Ashassins/NYAKB/ECE 362/ECE 362 Lectures/10-Advanced-Timers-Outputs.pdf

# Advanced Timers

# ECE 362 https://engineering.purdue.edu/ece362/

© 2021, Rick. All Rights Reserved. Redistribution Prohibited.

# Reading Assignment

# - Reading assignment:

– Textbook, Chapter 15, “General-purpose Timers”, pages 373 – 414.

# – Family Reference Manual, Chapter 17, "General

purpose timers (TIM2 and TIM3)", pages 377 – 443.

# Future Reading Assignment

- Textbook, Chapter 22, Serial Communication Protocols, pp. 527 – 598
– It’s a long chapter.
– Let’s first look at Section 22.3, SPI, pp. 568–577.
– Don’t worry so much about the USB section.
- Read that only if you’re curious.
- Your development board has no USB interface.
– There are some USB provisions in the STM32F091, but would take much work.
- Other books are better for understanding USB.

# GPIO Alternate Function

- Recall that the 2-bit fields in the GPIOx_MODER can take on four values to define a pin mode: – 00: Pin is an input.
– 01: Pin is an output.
– 10: Pin uses an alternate function.
– 11: Pin is an analog input.
- Today, we’ll start using the alternate function codes.
– Configured by four-bit fields in the GPIOx_AFRL and GPIOx_AFRH. – Datasheet, page 41, table 14, Alternate functions for Port A.
– Datasheet, page 42, table 15, Alternate functions for Port B.
– ...
- Configuring a pin for AF means you cannot use that pin for general purpose I/O. – See FRM, Figure 20, page 163.

# To set GPIO alternate function

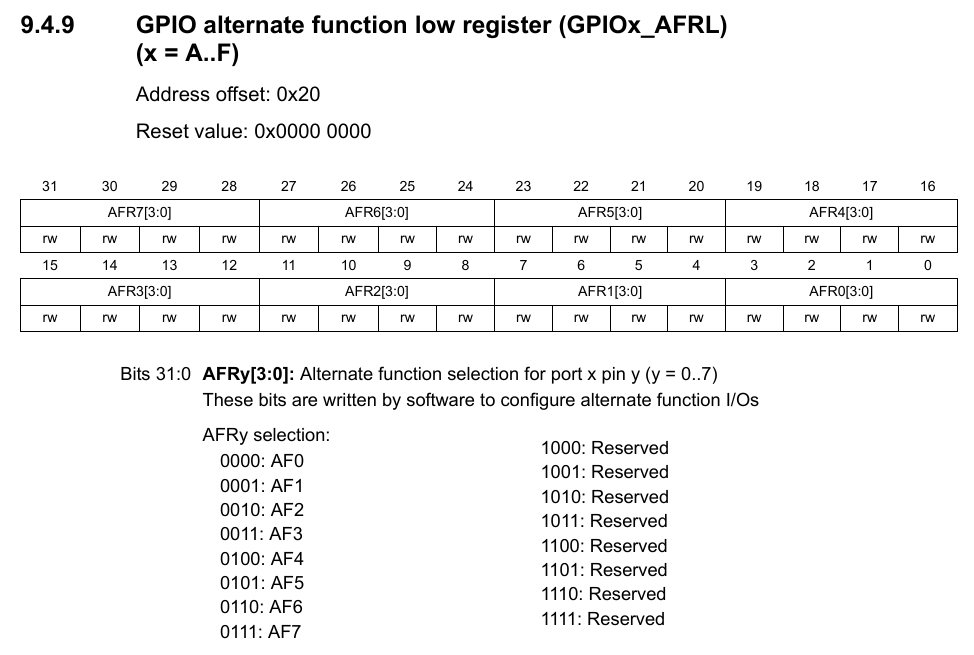
[picture p90: figure]

# - Two 32-bit AFR registers per port

named AFRL/AFRH.
- Four bits per pin.

## – e.g., to set PA0 to use timer 2, channel 1:

## - GPIOA->AFRL_AFR0[3:0] = 0010

– e.g., to set PB14 to use timer 15,

## channel 1:

## - GPIOB->AFRH_AFR6[3:0] = 0001

- (14 – 8 == 6)

## – Where did these numbers come from?

## - Tables 14 – 19

# Port A alt funcs: Datasheet pg 41

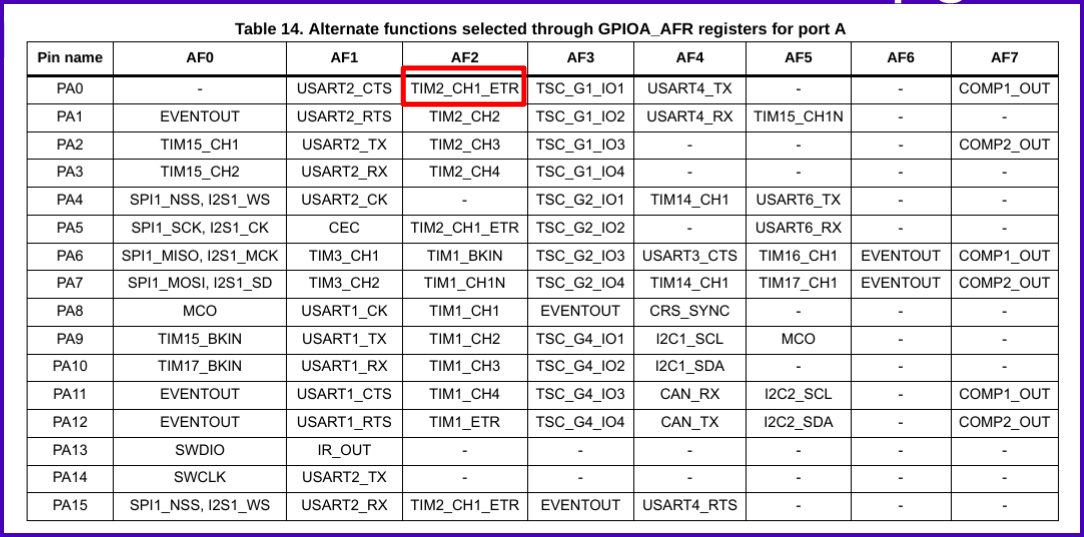
[picture p91: figure]

# Port B alt funcs: Datasheet, pg 42

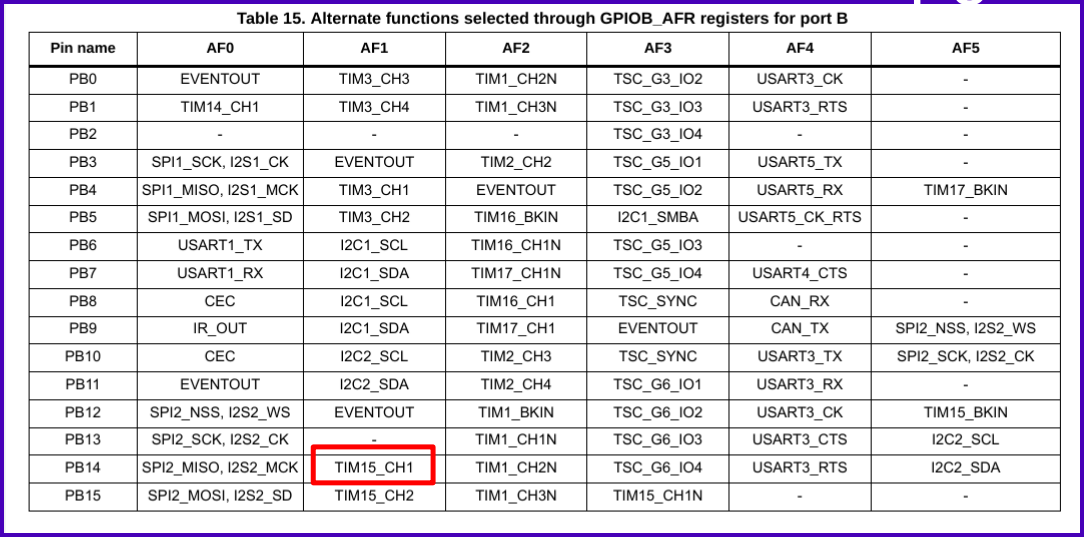
[picture p92: figure]

# Accessing AFRx registers with C

- It’s complicated.

# - You can refer to values with symbols like this:

# GPIO_AFRL_AFRL0 == 0x0000000F GPIO_AFRH_AFRH5 == 0x00F00000

# - It’s often easier to do it manually (e.g.: PB11: AF2):

# – GPIOB->AFR[1] &= ~(0xf << (4*(11-8))) – GPIOB->AFR[1] |= 0x2 << (4*(11-8))

# Timers: There are many

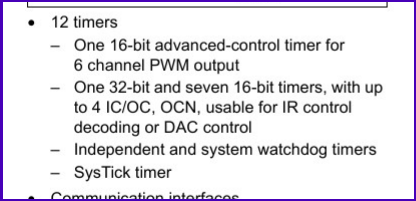
[picture p93: figure]

# - Start with the STM32F091xBC

datasheet page 1.

# “How should I choose?”

# - Start with the STM32F091xBC datasheet…

– page 34, table 13, pin definitions.
- See the "Alternate functions" column.

# – pages 41 – 44, table 14 – 19, Alternate functions for

Ports A, B, C, D, and F.

# – "What about Port E?"

- We don’t actually have a Port E on a 64-pin STM32F091.

# “If I want a certain function, how do I chose a pin for it?”

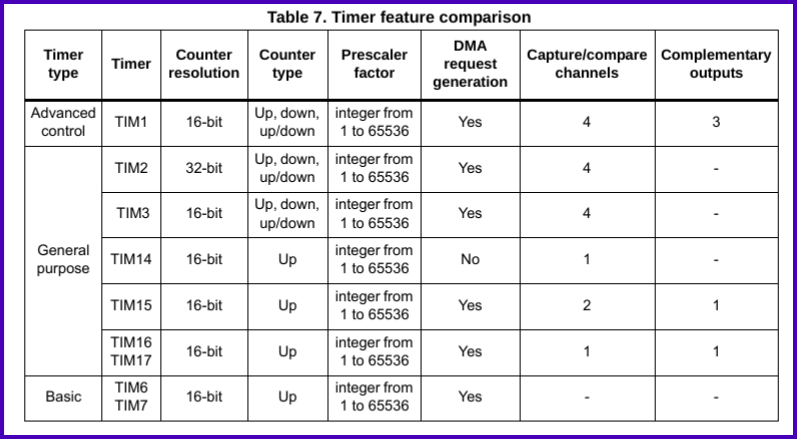
[picture p94: figure]

# - Start with the STM32F091xBC

datasheet again.

# – page 21, table 7, timer feature comparison

# “What pins should we start with?”

- From datasheet, table 13, pin definitions...

– User push button SW2 (PA0) can be connected to TIM2_CH1_ETR [Timer 2, channel 1 (and external trigger)] – Red LED (PC6) can be connected to TIM3_CH1 [Timer 3, channel 1] – Yellow LED (PC7) can be connected to TIM3_CH2 [Timer 3, channel 2] – Green LED (PC8) can be connected to TIM3_CH3 [Timer 3, channel 3] – Blue LED (PC9) can be connected to TIM3_CH4 [Timer 3, channel 4]
- So, let’s look at Timers 2 and 3.

# Timer groups 2 and 3

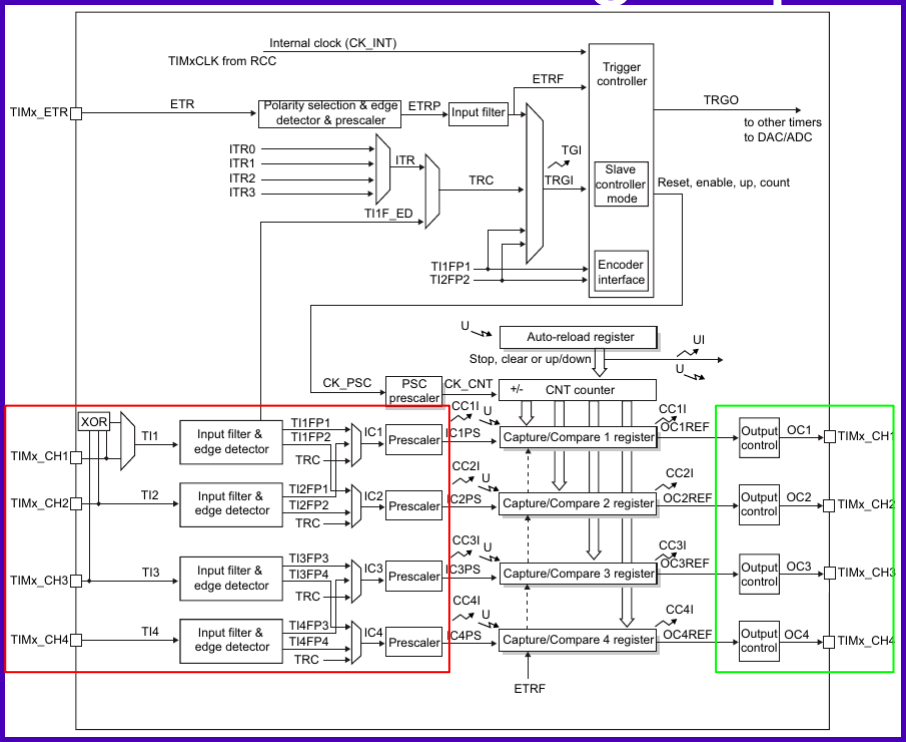
[picture p95: figure]

# - This is what either timer

2 or timer 3 look like.

# – Each one contains four

timer channels.

# - Each can:

## – measure input - count events - pulse length – generate output - toggle - PWM: Pulse Width Modulation – generate interrupts

# How do TIM2/TIM3 work?

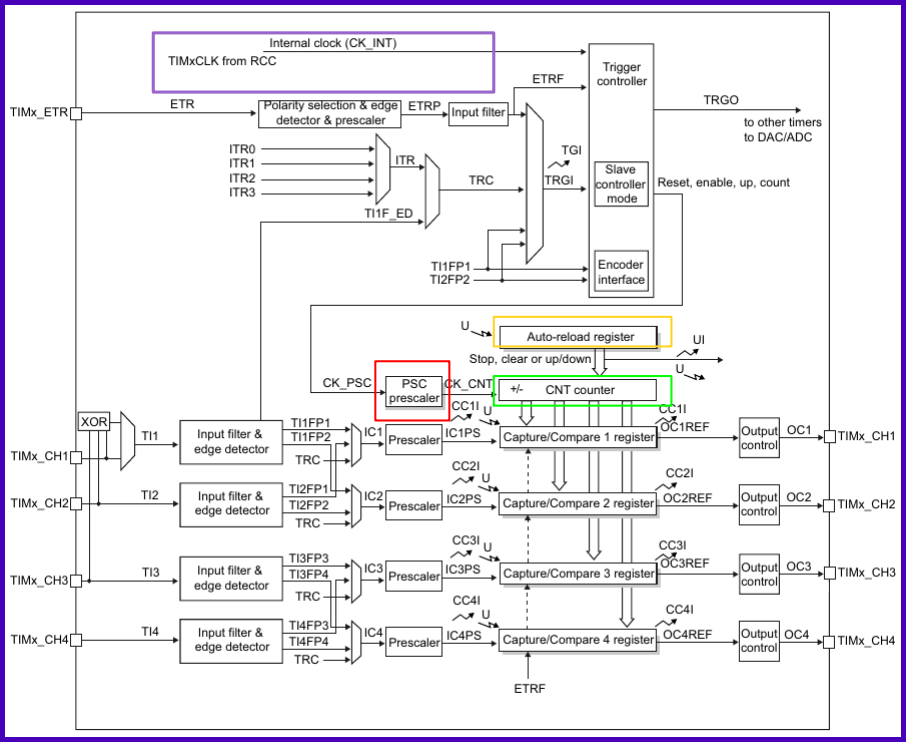
[picture p96: figure]

# - Each has a free-running counter (CTR) which is 16-

bit (TIM3) or 32-bit (TIM2).

# – 16-bit prescaler for input

clock (PSC).
- e.g. divide input clock by N.
- System clock is default clk.

# – Auto-reload register (ARR)

## - Can count up from 0 to ARR - Can count down from ARR to 0

- Can count up, down, up,

## down… 0 – ARR – 0 …

# Configuring a timer for "output"

# - Let’s look at output first. In this mode we:

# – configure a GPIO pin for an alternate function that connects it to a timer

rather than its ODR.

# – set up the prescaler (PSC) – set up the auto-reload register (ARR) – set the direction/mode of the counter (CR1 DIR) – set the output compare mode (CCMRn OCcM) – enable the "channel" the pin is connected to (CCER) – enable the timer’s counter (with the CR1 CEN bit)

# Counter modes

# ARR

# time ARR

# time ARR

# time

UP

# DOWN

# UP/DOWN

0

0

0

# Counter mode configuration

# - Set with the TIMx_CR1 register:

- CMS: Center-aligned (up/down) mode selection.
– Non-zero value enables up/down mode.

# - DIR: Direction: 0: counts up, 1: counts down

- CEN: Counter enable: 1: enable timer.

## – Set this one last. SET CEN LAST!

# How do channels work?

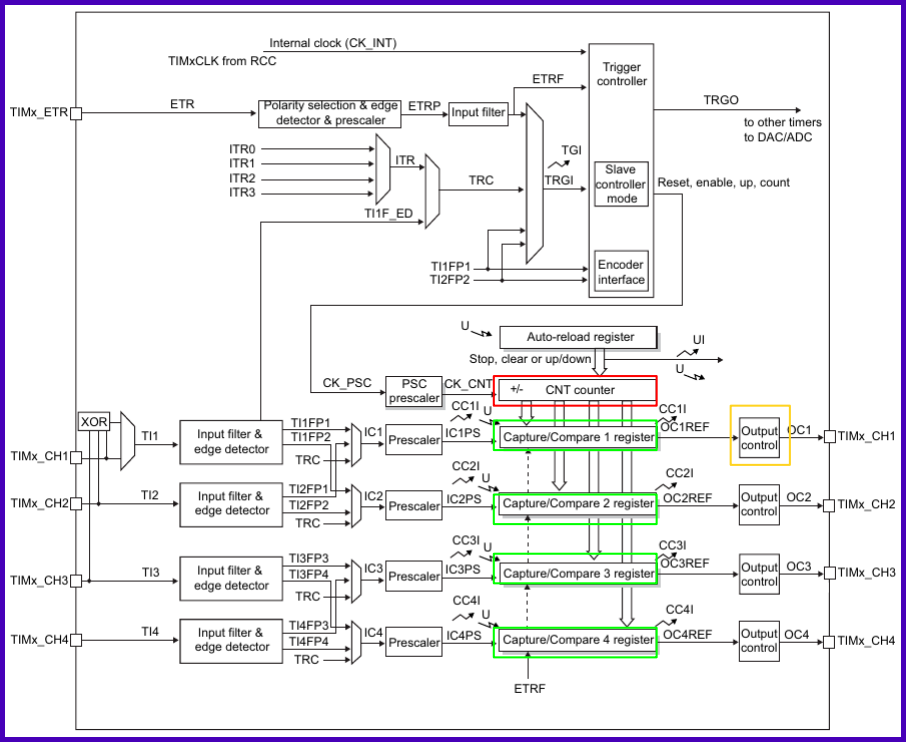
[picture p97: figure]

# - Each has a counter compare register

(CCRx).

# – Each is continually compared to the

counter (CTR).
– When CCRx = CTR,

# something happens to OCxREF (output

channel reference).

# Timer Output Modes

## - Configured with the two CCMRs (Capture/Compare Mode Registers)

## - CC1S: direction of channel:

– 00: output, 01: input mapped on TI1, 10: input mapped on TI2, 11: input mapped on TRC.

## - OC1M: output compare mode:

## – 001: Logic high if CNT = CCR – 010: Logic low if CNT = CCR – 011: Toggle if CNT = CCR – 110: PWM output mode 1: Logic high if CNT < CCR, else logic low

# Remember to enable the channels

# - Use the TIMx_CCER (capture/compare enable register)

# - CCxE: enable the channel

# Example: count up, active high

# ARR

# time

0

# CCRx

# time

0

# Output

# Each CCR is continually comparing its value

with the free-running counter.

# When it matches, the operation (go high) happens

# Example: count up, toggle mode

# ARR

# time

0

# CCRx

# time

0

# Output

# Each CCR is continually comparing its value

with the free-running counter.

# When it matches, the operation (toggle) happens

# Example: count up, toggle mode

# ARR

# time

0

# CCRx

# time

0

# Output

# Changing the CCRx value changes the offset

into the count when the output toggles.

# Example: up/down, toggle mode

# ARR

# time

0

# CCRx

# time

0

# Output

# Up/down mode is referred to as "Centered Mode"

# Example: up/down, toggle mode

# ARR

# time

0

# CCRx

# time

0

# Output

# Changing the CCRx value widens the active cycle of the wave, but it stays "centered"

# Example: count up, PWM mode 1

# ARR

# time

0

# CCRx

# time

0

# Output

# PWM output mode is an easy way of

configuring a variable "duty cycle" output.

# Example: count up, PWM mode 1

# ARR

# time

0

# CCRx

# time

0

# Output

# As CCRx value is decreased, the

"duty cycle" is decreased proportionally.

# How do I program this???

#include "stm32f0xx.h"

int main(void)
{
// Enable Port C
RCC->AHBENR |= RCC_AHBENR_GPIOCEN;

// Set the mode for PC8 for "alternate function" GPIOC->MODER &= ~(3<<16);
GPIOC->MODER |= 2<<16;

// Set the alternate function for PC8
// PC0-7 are on AFR[0], 8-15 are on AFR[1] GPIOC->AFR[1] &= ~0xf;
GPIOC->AFR[1] |= 0;

// Enable the system clock for timer 3 RCC->APB1ENR |= RCC_APB1ENR_TIM3EN;

// Counting direction: 0=up, 1=down
TIM3->CR1 &= ~TIM_CR1_DIR; // clear it to count up

// Set prescaler output to 4kHz (48MHz/12000) TIM3->PSC = 12000 – 1;

// Auto-reload 4000
TIM3->ARR = 4000 – 1;

// Any value between 0 and 4000.
TIM3->CCR3 = 3456;

// Channel 3 of the timer is configured in CCMR2. // Set the bits to select toggle mode (011) TIM3->CCMR2 &= ~TIM_CCMR2_OC3M_2; // Turn off bit 2.
TIM3->CCMR2 |= TIM_CCMR2_OC3M_1 | TIM_CCMR2_OC3M_0;

// Enable output for channel 3 active-high output TIM3->CCER |= TIM_CCER_CC3E;

// Enable timer 3
TIM3->CR1 |= TIM_CR1_CEN;

for(;;)
asm(“wfi”);

return 0;
}
Adapted from Textbook, page 380.

# This will blink the

green LED.

# Register summary

- See Family Reference Manual, table 60, page 442...

# - TIMx_CR1: Control Reg - TIMx_CCMR1/2: Capture/Compare Mode Reg - TIMx_CCER: Capture/Compare Enable Reg - TIMx_CNT: 16- or 32-bit Free-running counter - TIMx_PSC: 16-bit Prescaler Reg - TIMx_ARR: Auto-Reload Reg - TIMx_CCRx: Capture/Compare Reg

- RCC_APB1ENR: Location of the TIM3EN bit.

# Full view of Timer 2/3 again

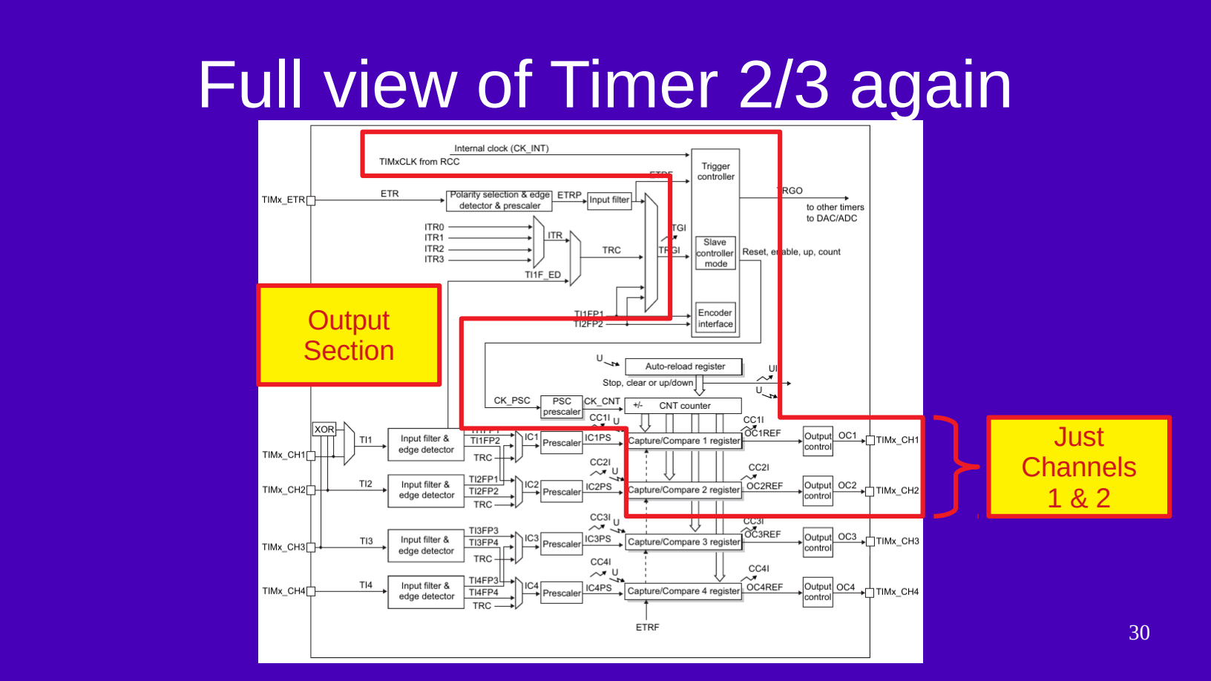
[picture p98: page 30]

# Output Section

# Just Channels

1 & 2

# Output config register arrangement

# Prescaler

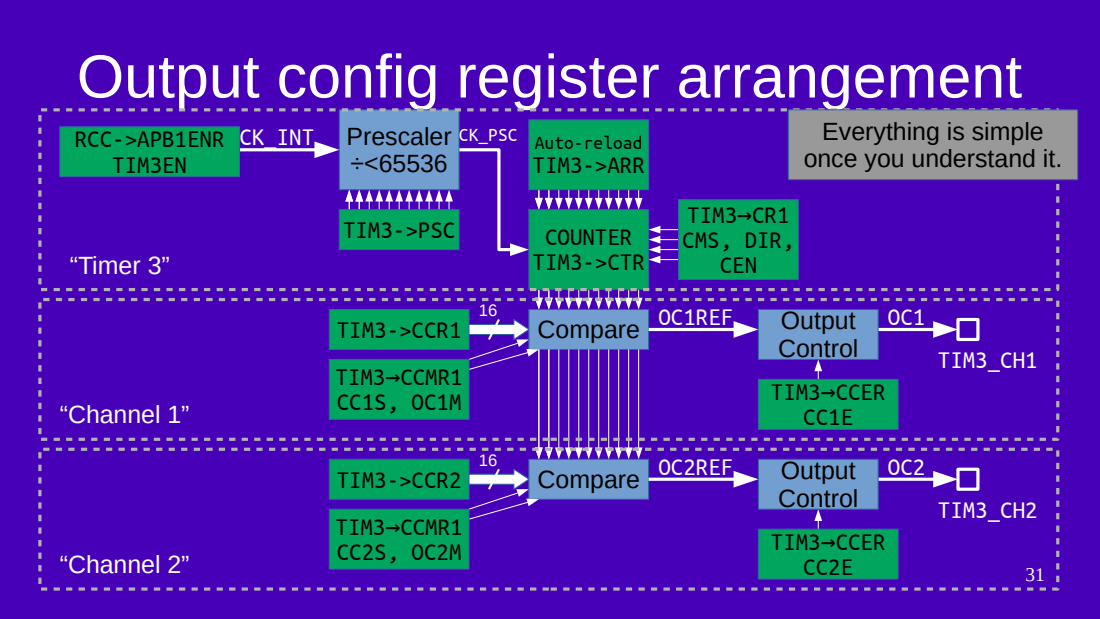
[picture p99: page 31]
CK_INT; CK_PSC; Auto-reload; TIM3->ARR; TIM3->PSC; COUNTER; TIM3->CTR; TIM3 CR1 →CR1 CMS, DIR, CEN; TIM3->CCR1; Compare; TIM3 CCMR1 →CR1 CC1S, OC1M; OC1REF ¹⁶; RCC->APB1ENR TIM3EN; TIM3 CCER →CR1 CC1E; Output Control; TIM3_CH1; TIM3->CCR2; TIM3 CCMR1 →CR1 CC2S, OC2M; OC2REF ¹⁶; TIM3 CCER →CR1 CC2E; TIM3_CH2; “Timer 3”; “Channel 1”; “Channel 2”

Everything is simple
once you understand it.
