Ashassins/NYAKB/ECE 362/ECE 362 Lectures/12-DAC.pdf

Digital-to-Analog Conversion

ECE 362
https://engineering.purdue.edu/ece362/

© 2021, Rick. All Rights Reserved. Redistribution Prohibited.

Reading Assignment

- Textbook, Chapter 21, Digital-to-Analog Conversion, pp. 507 – 526. – Read this first.
- FRM, Chapter 14, Digital-to-analog converter (DAC), pp. 269 – 281. – Scan. Learn basics like I/O registers, enabling, use.
- Textbook, Chapter 20, Analog-to-Digital Conversion, pp. 481 – 506. – Read this later.
- FRM, Chapter 13, Analog-to-Digital converter (ADC), pp. 229 – 268. – Scan this later. Learn basics like I/O registers, enabling, use.

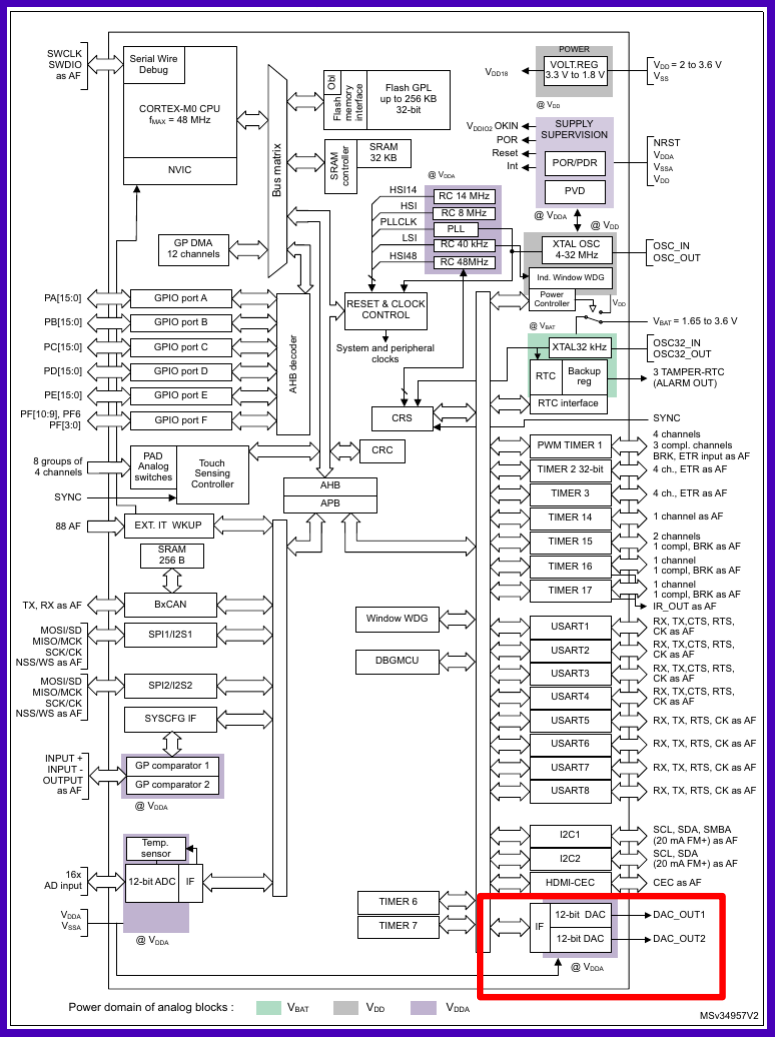
[picture p113: figure]

The STM32F091

- Digital-to-Analog Converter
– 2 external channels (DAC_OUT1, DAC_OUT2)
- What pins are those?
– You can look those up. You know how. – Or pay close attention to the lecture.
– 0 – 3.6V conversion range
- Our voltage reference is about 3.0V – 12-bit resolution, by default
- 8-bit resolution too
– right-aligned (default) or left-aligned

DAC Block Diagram

Page 270 of the

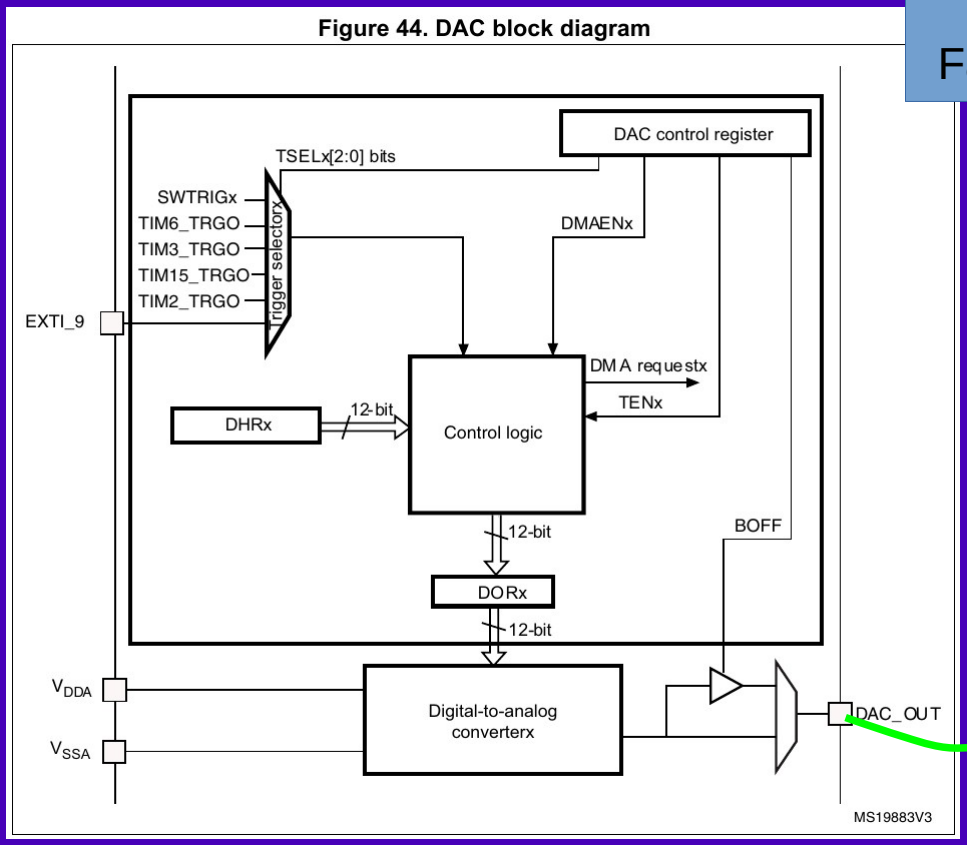
[picture p114: figure]

Family Reference Manual

- A Data Output Register (DORx) holds a value that is converted to an analog voltage between 0 and 3V.
- CPU can’t write directly to DORx.
- Must write to DHRx.
– "Data Holding Register"
– A trigger will move DHRx to DORx.

DAC Output Connection

- Some analog pin(s) can be output.

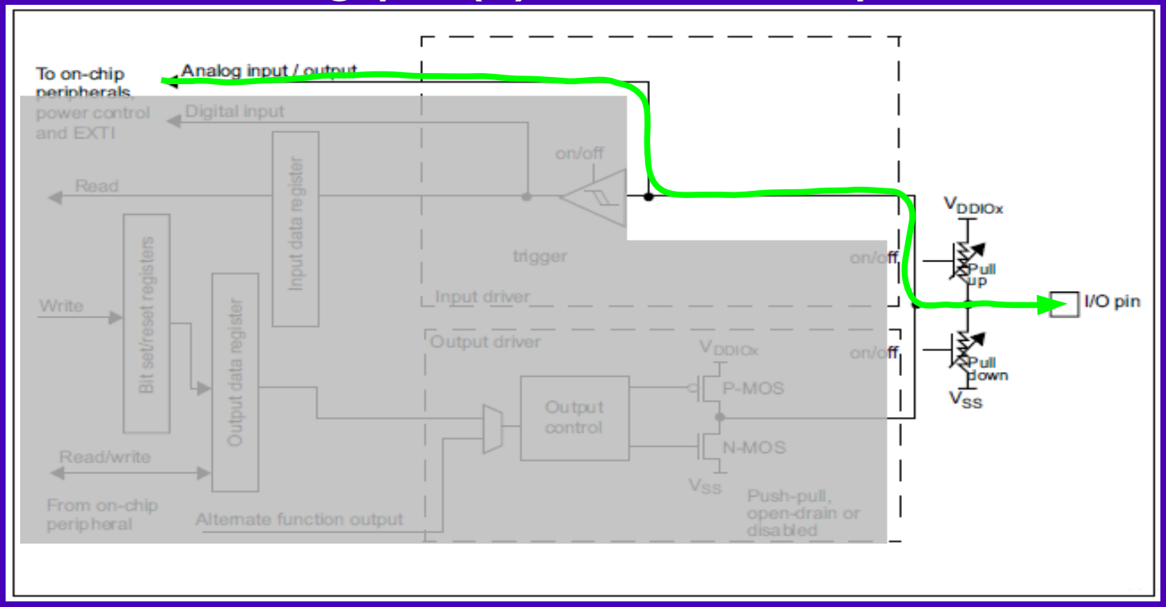
[picture p115: figure]

Port MODER

- 16 2-bit values determine, input, output, or special operation. – 00: Port pin is used for input
– 01: Port pin is used for output
– 10: Port pin has an alternate function
– 11: Port pin is an analog pin

How does a DAC work?

- And what does this left-aligned or right-aligned mean?

Let’s talk about number systems

- A group of bits can be used to represent arbitrary things
- A character, a number, an image, …
- "Integers" have a well-known format
128 | 64 | 32 | 16 | 8 | 4 | 2 | 1
0 | 1 | 0 | 1 | | 1 | 0 | 1
... | 1
= 93
- Ellipsis goes off to the left.
- What if we added another bit to the right?

Binary fractions

- We can let a 16-bit value represent anything we want, so let’s let the upper 8 bits represent an integer, and let the lower 8 bits represent fractional powers of 2
- The dot is called a "binary point"
- Representation, below, is called "fixed point", Q8.8, or just Q8.

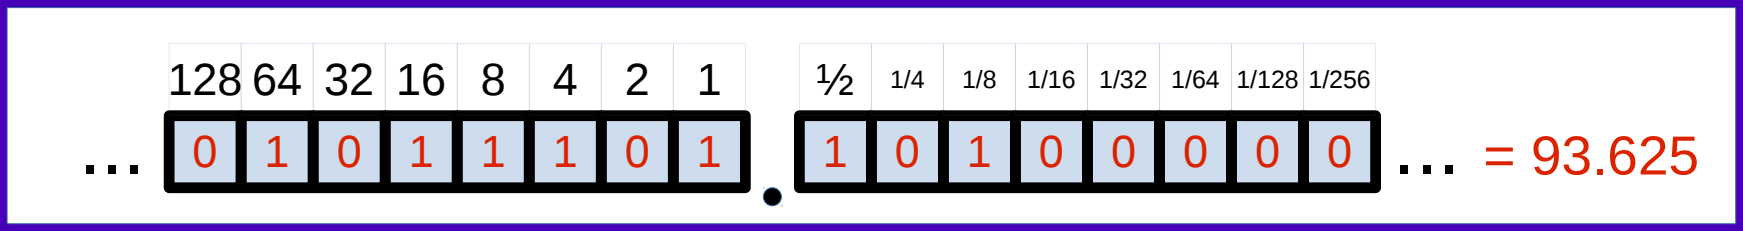
[picture p116: figure]

- Standard binary addition and subtraction still works.
- Multiplication needs a correcting shift afterward.

Fixed point is inexact

- Sums of fractional powers of 2, OK.
– e.g. We can express 3.75 as 00000011.1100….
- Anything else has rounding errors. e.g. 93.1.
- 93 + 1/8 is 93.125 (too big)
- 93 + 1/16 + 1/32 = 93.9375 (too small)
- 93 + 1/16 + 1/32 + 1/256 + 1/512 = 93.099609375 (too small, but closer)

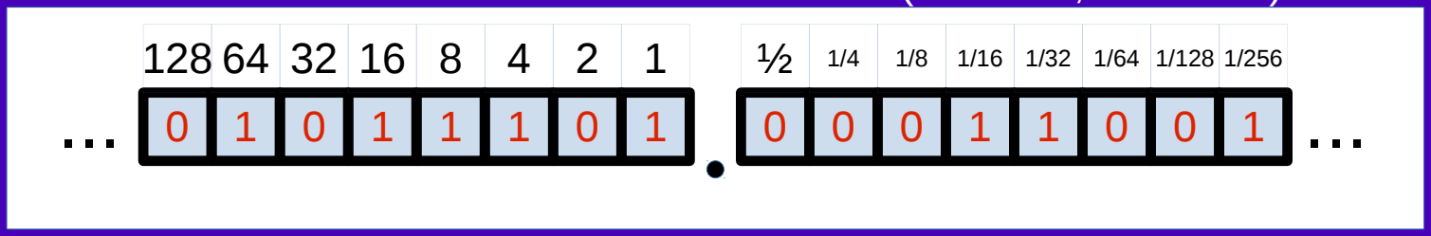
[picture p117: figure]

- The precise binary value would repeat forever: 01011101.000110011001100...

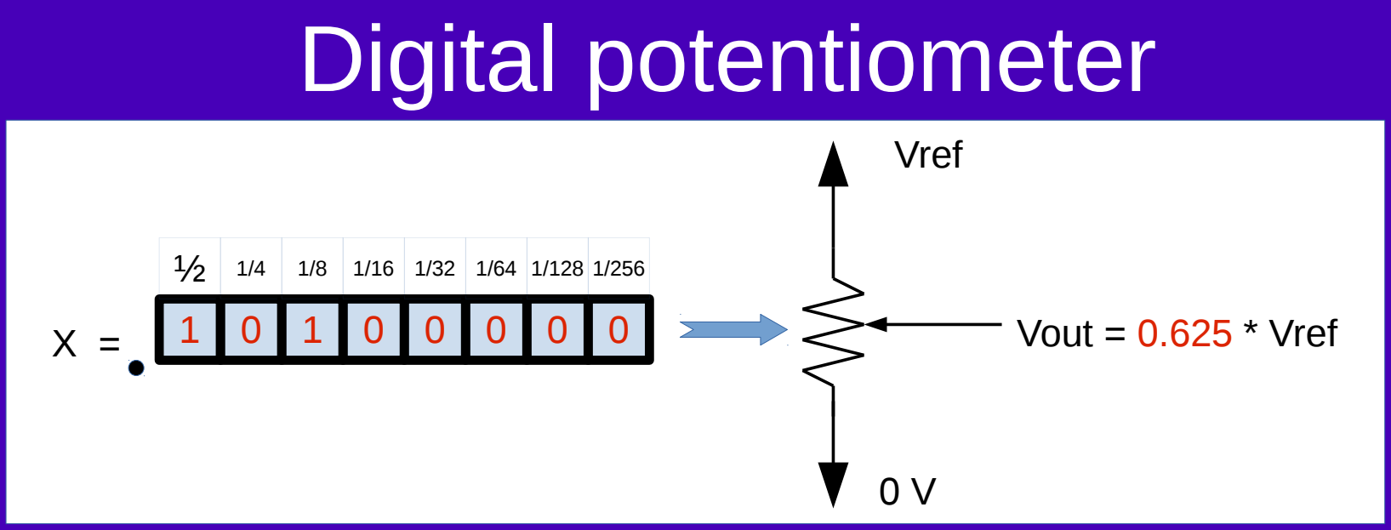
[picture p118: figure]
Digital potentiometer; Vref; Vout = 0.625 * Vref

- We want hardware that can convert a binary fraction to a voltage.
– The most significant bit of the fraction is “worth” half the reference voltage. – A “left-aligned” conversion value is, effectively, a binary fraction.
- How can we build such a thing?

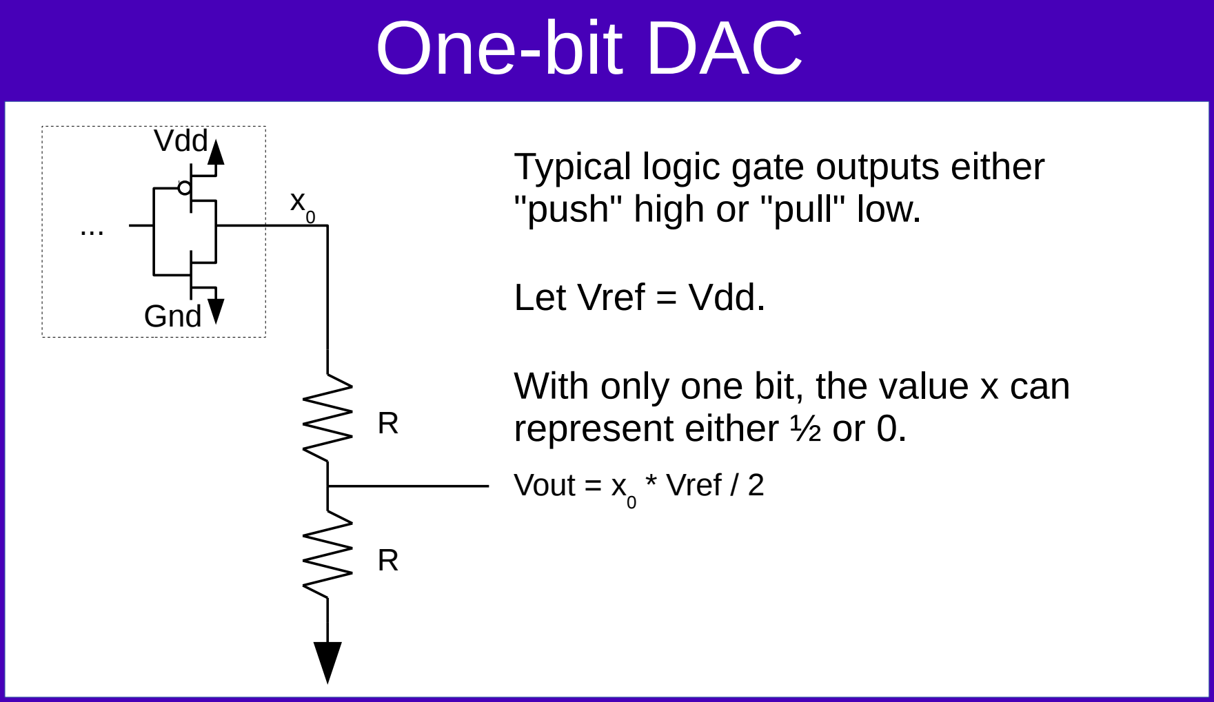
[picture p119: figure]
One-bit DAC; Vout = x; * Vref / 2; Typical logic gate outputs either "push" high or "pull" low.; Let Vref = Vdd.; With only one bit, the value x can represent either ½ or 0.; Vdd; Gnd

Two-bit DAC

- X can have the values 0, ¼, ½, or ¾.

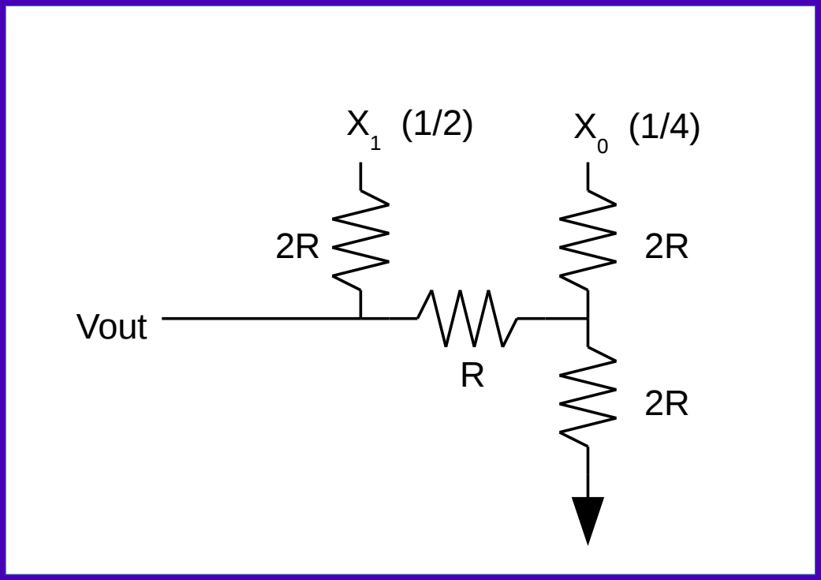
[picture p120: figure]
Vout

Many-bit DAC

- Add N more bits by adding N more R-2R resistors...

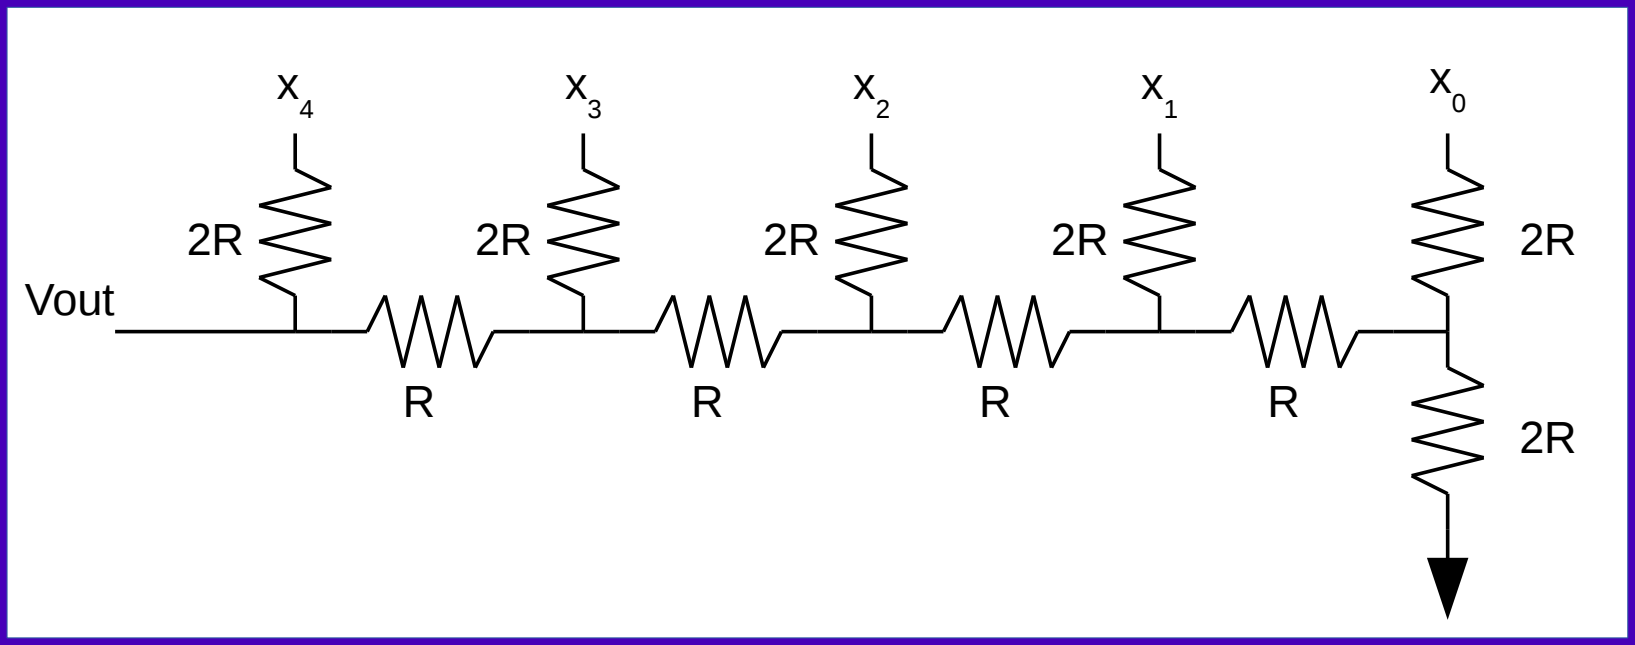
[picture p121: figure]
Vout

– This is called an R-2R resistor ladder.

DAC: How fast is the conversion?

- Speed of light.
– Some settling time required due to capacitance (and inductance) in circuit.
– Small glitches may be present due to differences in delays for turning on and off inputs into the resistor network.
- No iteration or convergence needed.

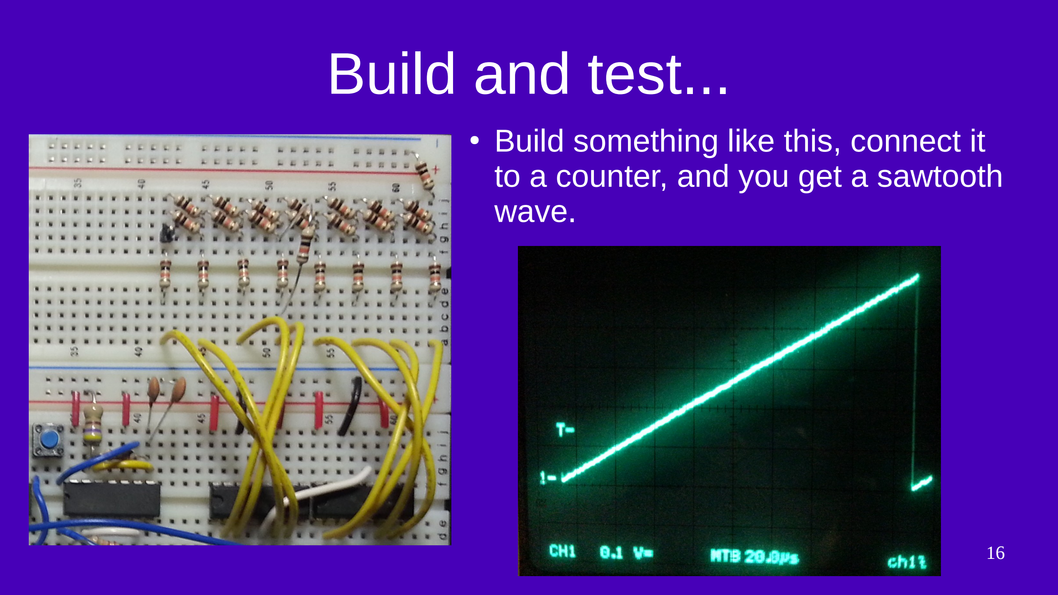
[picture p122: page 16]

Build and test...

- Build something like this, connect it to a counter, and you get a sawtooth wave.

Limits of DAC resolution

- Resistor tolerance is a limitation.
- Linearity of the output is only as good as the correctness of the resistor ratios.
- A single errant resistor can be problem.
- Small deviation will cause small error.
- Large deviation causes a non-monotonic output for the sawtooth wave.
- To ensure a monotonic sawtooth, each resistor should be less than +/- 1/(2N) its listed value. Why?
– Consider transition from 01111 to 10000.

●

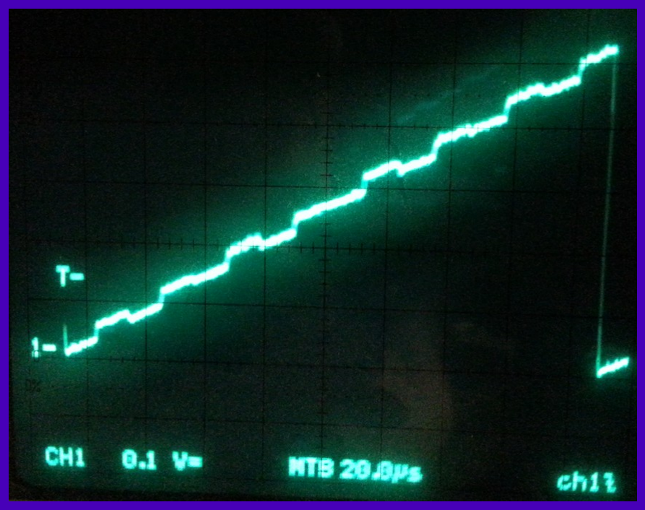
[picture p123: figure]

If most significant resistor was off by -1/(2⁵) the two values would be the same. – For an 8-bit DAC, resistor error must be < 0.4%
– For a 12-bit DAC, resistor error must be < 0.024%
- Helps if all resistors are on same silicon substrate!
– Which is what you have on your microcontroller.

Using the STM32 DAC

- There are two DACs on the STM32F091RCT6. – That can be used with two channels / pins.
- Cannot write directly to a DAC output register. – Instead, write a digital value to one of three "data holding registers."
– Some kind of trigger will copy it to the output register.

DAC Holding Registers

- 8-bit or 12-bit
- left-aligned or right-aligned
| xxxxxxxxxxxx

xxxxxxxxxxxx

| xxxxxxxx
31 | 23 | 15 | 7 | 0

DAC_DHR8R1: 8-bit, right-aligned, ch1

DAC_DHR12L1: 12-bit, left-aligned, ch1

DAC_DHR12R1: 12-bit, right-aligned, ch1

DAC Triggers

- Seven different trigger possibilities – 5 timers
– EXTI line9
– Software trigger
- Set with the DAC->CR TSEL1/2 fields. – 111 is the software trigger. Use this for now.

To trigger the DAC with a
software trigger
- Wait while the channel trigger is set. Once it is clear:
– Write a new value to a holding register.
– Set the trigger bit.

Example code to generate a sawtooth wave

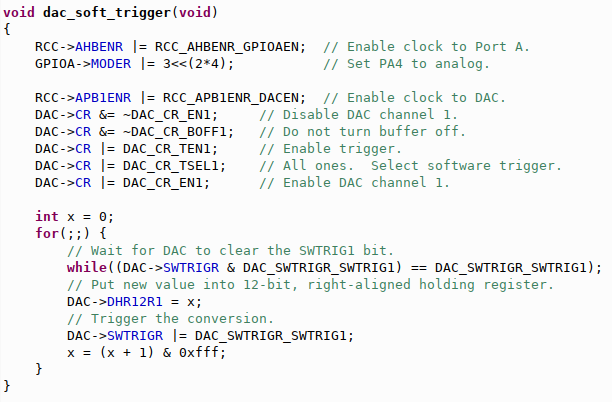
[picture p124: figure]

Scope view of unloaded pin

- 10x probes.
- 0.5V/div
- 500μs/div
- slight curve
on lower end

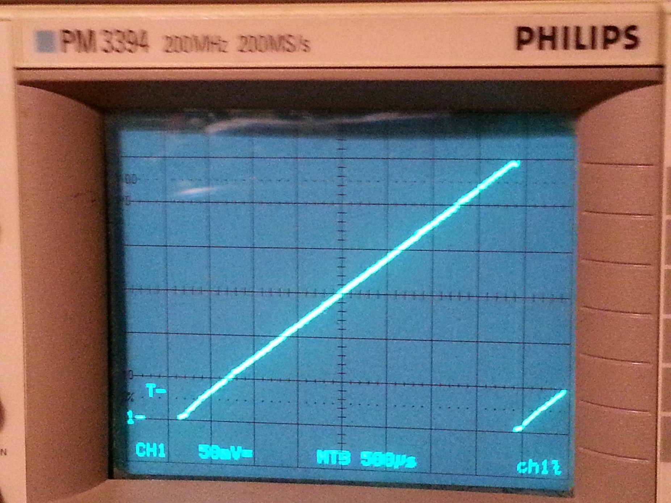
[picture p125: figure]

Conversion Examples

- Assume that VREF is 3.0 V.
- If the DAC’s right-aligned 12-bit data holding register was given the following values, what would the analog output voltage be?
- 0 ?
- 4095 ?
- 2047 ?
- 1023 ?

Output linearly related to DAC value

- Generally, the DAC output will be:

VOUT = VREF * N
4096

Some differences

- Lecture explanation of a DAC differs from that of the textbook and the FRM.
– Lecture: Each increment of the DAC value represents 1/4096th of VREF
- Minimum: 0 * VREF
- Maximum: 4095/4096 * VREF
– FRM: Each increment of the DAC value represents 1/4095th of VREF
- Minimum: 0 * VREF
- Maximum: 4095/4095 * VREF

Does this difference matter?

- The difference between the lecture and textbook version of a DAC is 1/4096th VREF – or about 0.024%. But nothing is exact... – There are deviations from linearity for the DAC.
– There is often a noise problem with the analog subsystems of the STM32F0.
- It’s about 0.02%. (More about this when we talk about ADC)
- Difference between this lecture and text doesn’t matter.
– You won’t notice a range of [0 – 2.9928] instead of [0 – 3.0]

What is BOFF1?

- An output buffer
can be turned off.
- You probably want
to leave it turned
on:
- DAC->CR &= ~
DAC_CR_BOFF1;

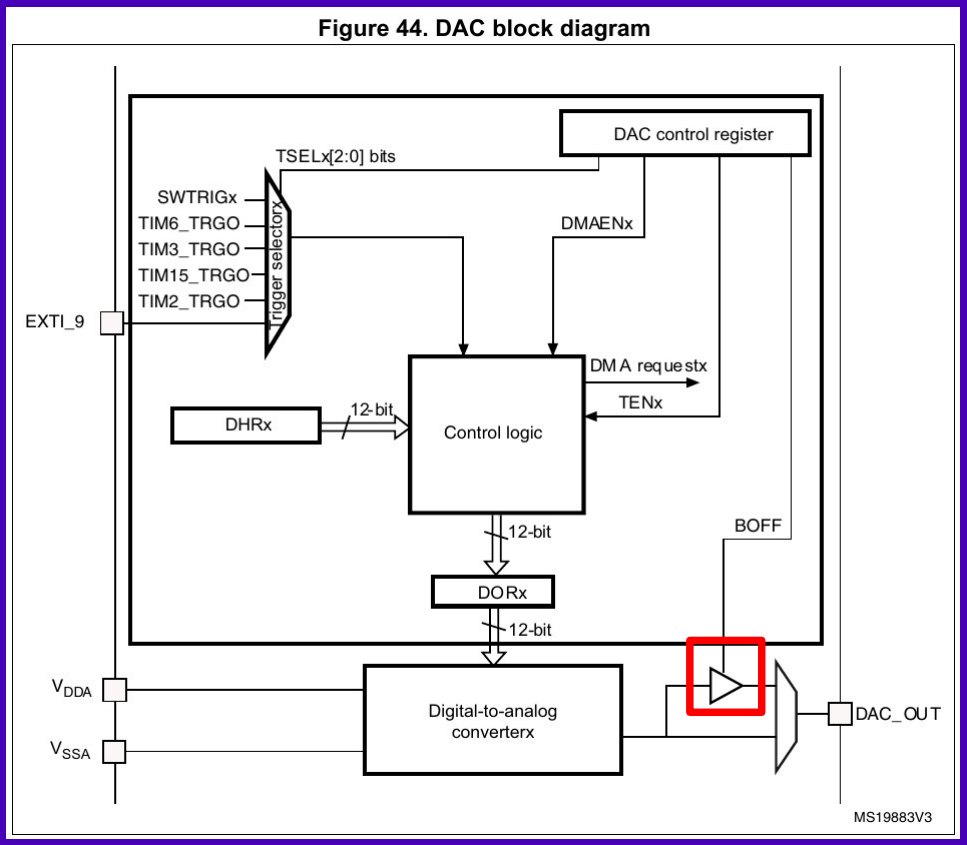
[picture p126: figure]

Why do we need a buffer?

- Recall the hand-built DAC circuit:

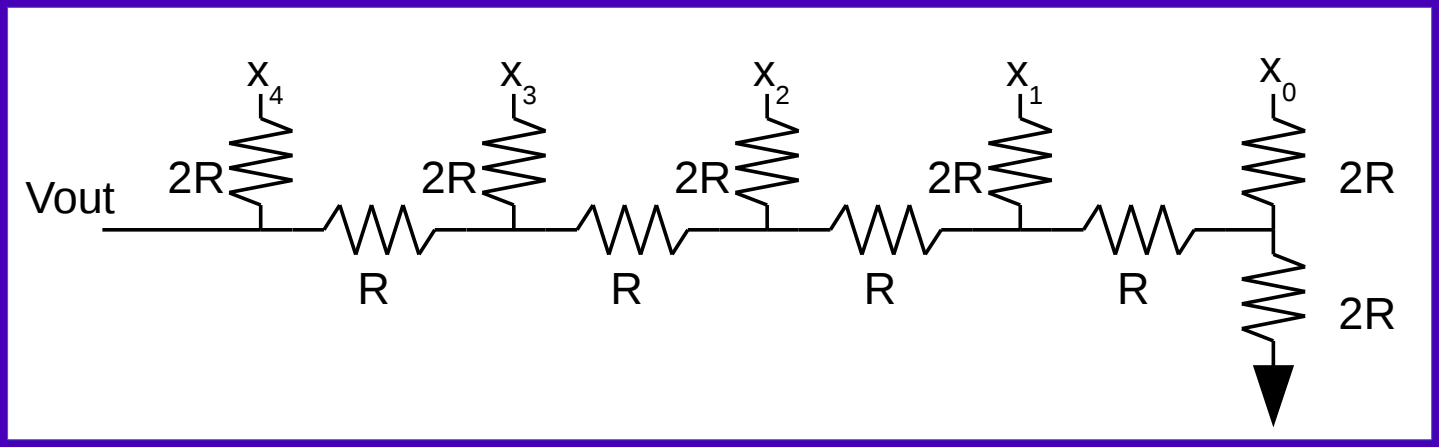
[picture p127: figure]
Vout

- What’s the impedance of Vout if R = 10KΩ?

Why would we turn buffer off?

- Maybe you want to use your own high-precision amplifier?
– Remember that small curve on the low end of the scope view.

DAC uses

- We can use the DAC for slow things:
– process control, object location manipulation by voltage, etc.
- The DAC can be updated very quickly.
– More than 100k/sec.
– This is useful for producing audio.
– One example is a sine wave table.

What is a sine table?

- We saw that writing monotonically-increasing values to the DAC produced a sawtooth wave.
- Imagine a set of 16 samples that look like this, that are sent repeatedly:
- BTW: For a large wave table, we make it "const". Why?

4095

2047

0

What is the frequency of the wave?

- We can see that this looks like a fuzzy sinusoid. – How do we calculate the frequency?
– Sample/sec / Number of samples in a cycle
– For 64k samples/sec, 16 samples/cycle…

– 4 kHz

4095

2047

0

Demonstration 1: Raw output

- First circuit:
- First, try square waves with GPIO.
- Next, try DAC sawtooth, square wave.

STM32

PA4

10μF
+

What’s the large capacitor for?

Ensuring that a constant
voltage on pin does not result in a constant current flowing through the speaker coil.

8Ω

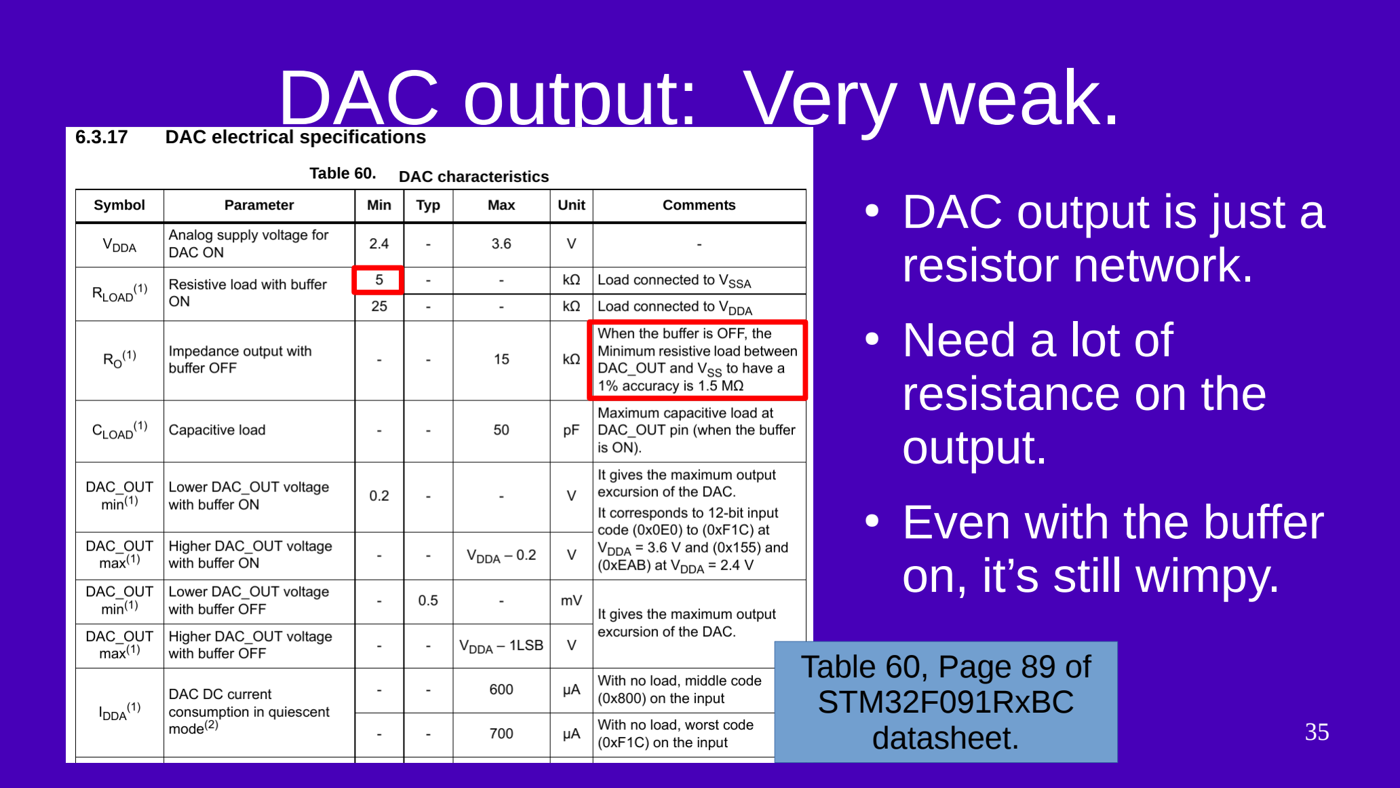
[picture p128: page 35]

DAC output: Very weak.

- DAC output is just a
resistor network.
- Need a lot of
resistance on the
output.
- Even with the buffer
on, it’s still wimpy.

Table 60, Page 89 of
STM32F091RxBC
datasheet.

Table 60.

Demonstration 2: Amplified output

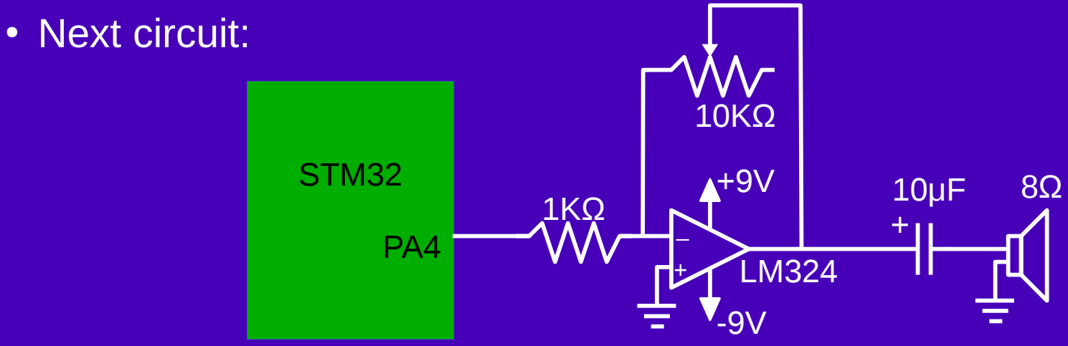
[picture p129: figure]
● Next circuit:; STM32

- DAC sawtooth again, square waves.
- Sine table.

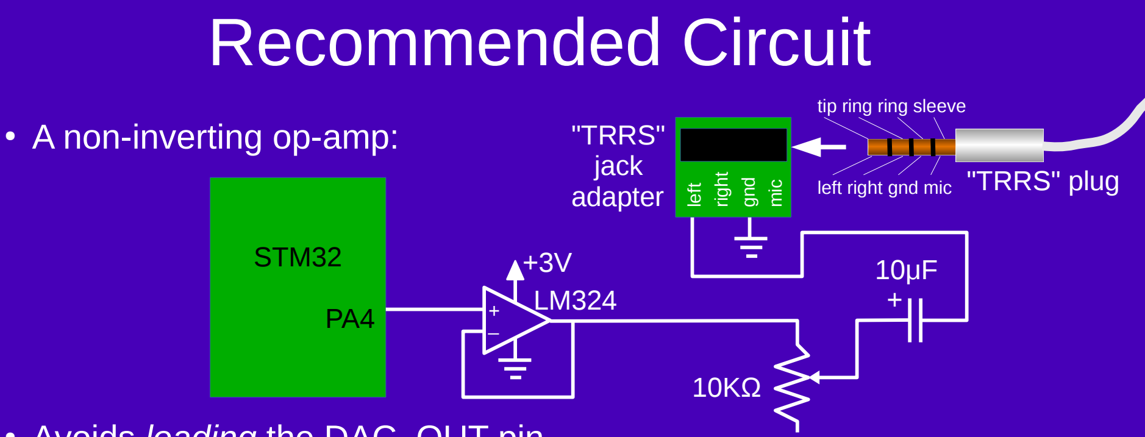
[picture p130: figure]
Recommended Circuit; ● A non-inverting op-amp:; STM32; "TRRS" jack; adapter; left; rig; mic; tip ring ring sleeve; left right gnd mic "TRRS" plug

- Avoids loading the DAC_OUT pin
- Protects the analog circuitry of the microcontroller

Protect the analog circuitry of the microcontroller!
- CAUTION: When you configure a pin on the STM32 for analog operation, you connect that pin to sensitive electronics inside the chip.
- If that pin is connected to voltage higher than 4V for just an instant, it will permanently, irreversibly damage either the pin or the entire microcontroller.
