Ashassins/NYAKB/ECE 362/ECE 362 Labs/lab1/main.c

.cpu cortex-m0
.thumb
.syntax unified
.fpu softvfp

.global login
login: .asciz "subbiah"

.align 2
.global main
main:
    bl   autotest // Uncomment this ONLY when you're not manually invoking below.
    movs r0, #1
    movs r1, #2
    movs r2, #4
    movs r3, #8
    bl   example // invoke the example subroutine
    nop

    movs r0, #96
    negs r0, r0 // replace these values with examples from the prelab
    movs r1, #4
    negs r1, r1
    movs r2, #40
    movs r3, #61
    negs r3, r3
    bl   step31 // invoke Step 3.1
    nop

    movs r0, #28 // replace these values with examples from the prelab
    negs r0, r0
    movs r1, #3
    negs r1, r1
    movs r2, #52
    movs r3, #14
    bl   step32 // invoke Step 3.2
    nop

    movs r0, #77 // replace these values with examples from the prelab
    negs r0, r0
    movs r1, #94
    movs r2, #75
    movs r3, #56
    bl   step33 // invoke Step 3.3
    nop

    movs r0, #92 // replace these values with examples from the prelab
    negs r0, r0
    movs r1, #83
    movs r2, #97
    movs r3, #83
    negs r3, r3
    bl   step41 // invoke Step 4.1
    nop

    movs r0, #34
    movs r1, #32
    movs r2, #70 // replace these values with examples from the prelab
    negs r2, r2
    movs r3, #54
    bl   step42 // invoke Step 4.2
    nop

    movs r0, #0 // unused as an input operand
    movs r1, #16
    movs r2, #2
    movs r3, #3
    bl   step51 // invoke Step 5.1
    nop

    movs r0, #5
    bl   step52 // invoke Step 5.2
    nop


    bl   setup_portc
loop:
    bl   toggle_leds
    ldr  r0, =500000000
wait:
    subs r0,#83
    bgt  wait
    b    loop

// The main function never returns.
// It ends with the endless loop, above.

// Subroutine for example in Step 3.0
.global example
example:
    // Enter your code here
    adds r1, r0, r1
    adds r1, r1, r2
    adds r1, r1, r3
    movs r0, r1
    bx   lr

// Subroutine for Step 3.1
.global step31
step31:
    // Enter your code here
    adds r0, r0, r1
    subs r2, r2, r3
    muls r0, r0, r2
    bx   lr

// Subroutine for Step 3.2
.global step32
step32:
    // Enter your code here
    subs r2, r2, r3
    negs r0, r0
    adds r0, r0, r1
    muls r0, r2, r0
    bx   lr

// Subroutine for Step 3.3
.global step33
step33:
    // Enter your code here
    subs r3, r3, r2
    subs r1, r1, r0
    subs r0, r3, r1
    bx   lr

// Subroutine for Step 4.1
.global step41
step41:
    // Enter your code here
    orrs r3, r0
    ands r1, r2
    movs r0, r3
    orrs r3, r1
    ands r0, r1
    bics r3, r0
    movs r0, r3
    bx   lr

// Subroutine for Step 4.2
.global step42
step42:
    // Enter your code here
    movs r2, #0x6e
    movs r3, #0x87
    ands r0, r2
    bics r1, r3
    subs r0, r0, r1
    bx   lr

// Subroutine for Step 5.1
.global step51
step51:
    // Enter your code here
    lsls r3, r3, r1
    lsrs r3, r3, r2
    movs r0, r3
    bx   lr

// Subroutine for Step 5.2
.global step52
step52:
    // Enter your code here
    movs r1, #0x1
    movs r2, #5
    bics r0, r1
    lsls r0, r0, #3
    orrs r0, r2
    bx   lr

// Step 6: Type in the .equ constant initializations below
.equ RCC,			0x40021000
.equ AHBENR,		0x14
.equ GPIOCEN,		0x00080000
.equ GPIOC,			0x48000800
.equ MODER,			0x00
.equ ODR,			0x14
.equ ENABLE6_TO_9,	0x55000
.equ PINS6_TO_9,	0x3c0

.global setup_portc
setup_portc:
    // Type in the code here.
    // Enable the RCC clock for the GPIOC peripheral
    ldr  r0, =RCC
    ldr  r1, [r0,#AHBENR]
    ldr  r2, =GPIOCEN
    orrs r1, r2
    str  r1, [r0,#AHBENR]

    // Set pins 6 through 9 to be outputs
    ldr  r0, =GPIOC
    ldr  r1, [r0,#MODER]
    ldr  r2, =ENABLE6_TO_9
    orrs r1, r2
    str  r1, [r0, #MODER]
    // Return
    bx   lr

.global toggle_leds
toggle_leds:
    // Type in the code here.
    // Read and toggle all four pins
    ldr  r0, =GPIOC
    ldr  r1, [r0,#ODR]
    ldr  r2, =PINS6_TO_9
    eors r1, r2
    str  r1, [r0,#ODR]
    bx   lr
